NCAR/openiotwx-stl/shield/pineapple_shield_MF.stl

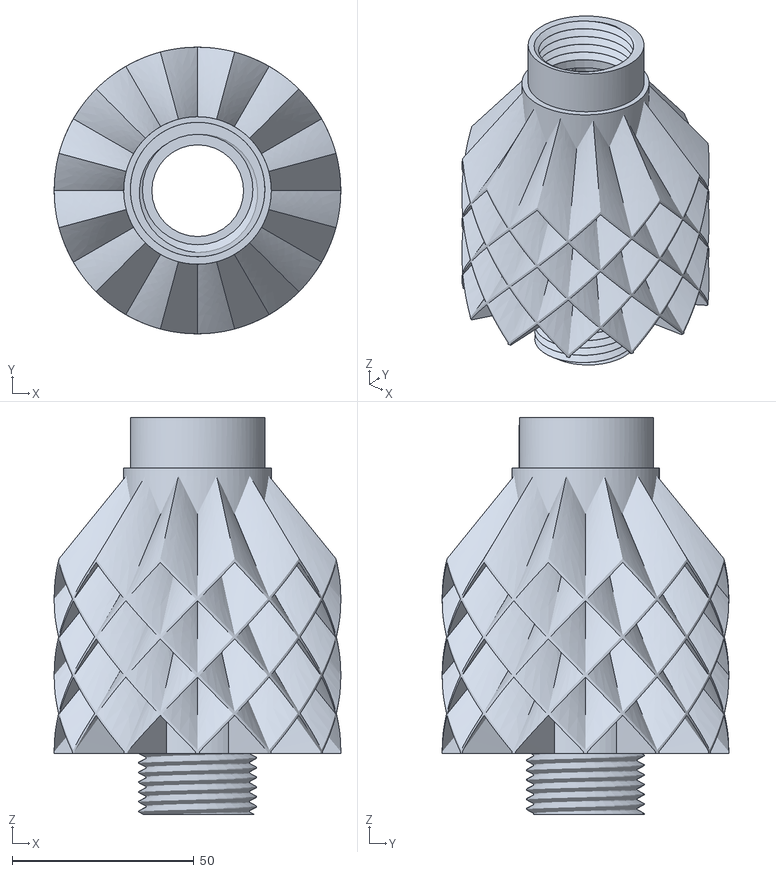
[picture p15: CAD file, 2023-07-29]
shield/pineapple_shield_MF.stl
78.9 x 78.9 x 109.2
