NCAR/openiotwx-stl/uv/uv_tube_F.stl

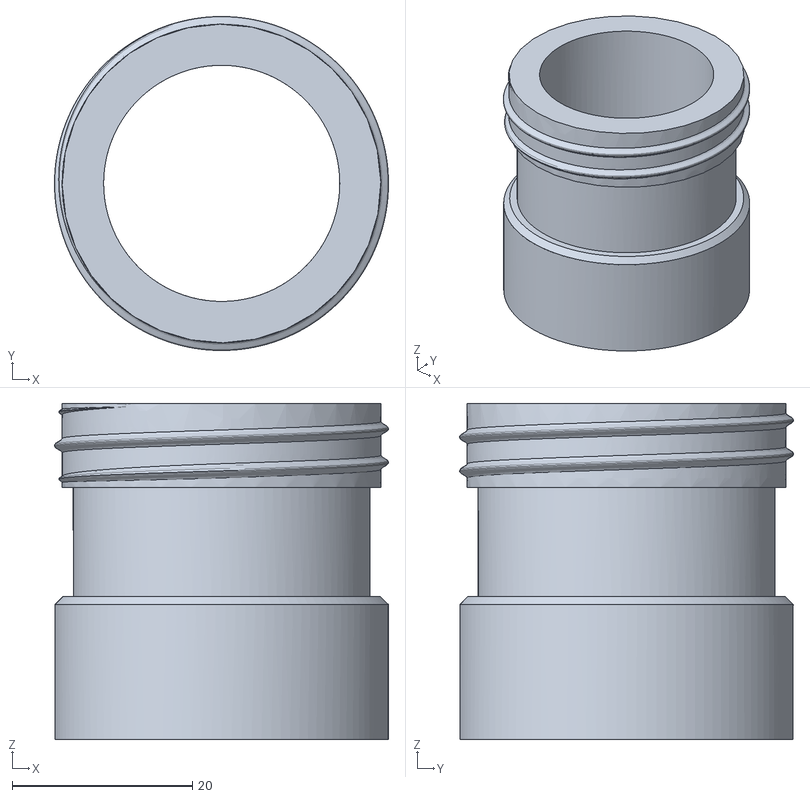
[picture p16: CAD file, 2023-07-29]
uv/uv_tube_F.stl
37.1 x 37.1 x 37.3
