NCAR/openiotwx-stl/accessories/sensor_stand/Center Column.stl

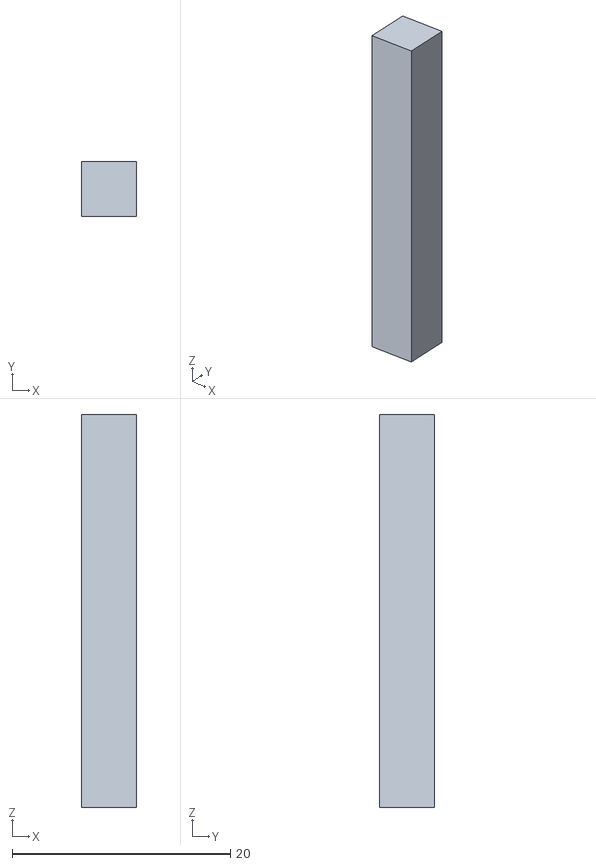
[picture p17: CAD file, 2024-05-13]
accessories/sensor_stand/Center Column.stl
5.00 x 5.00 x 36.0
