NCAR/openiotwx-stl/aq/aq_base_F.stl

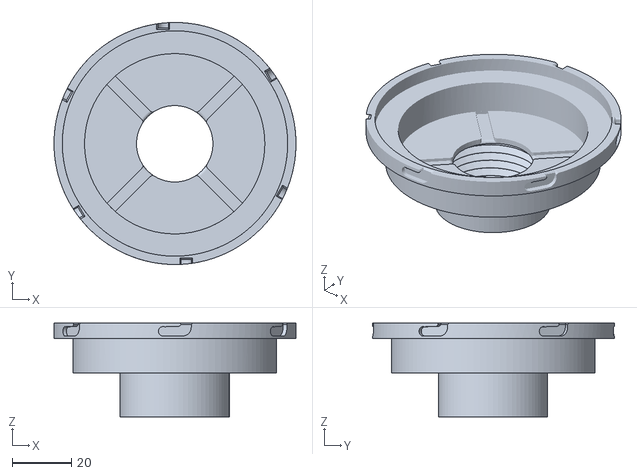
[picture p18: CAD file, 2023-07-29]
aq/aq_base_F.stl
81.9 x 81.9 x 31.8
