NCAR/openiotwx-stl/endcaps/vented_endcap.stl

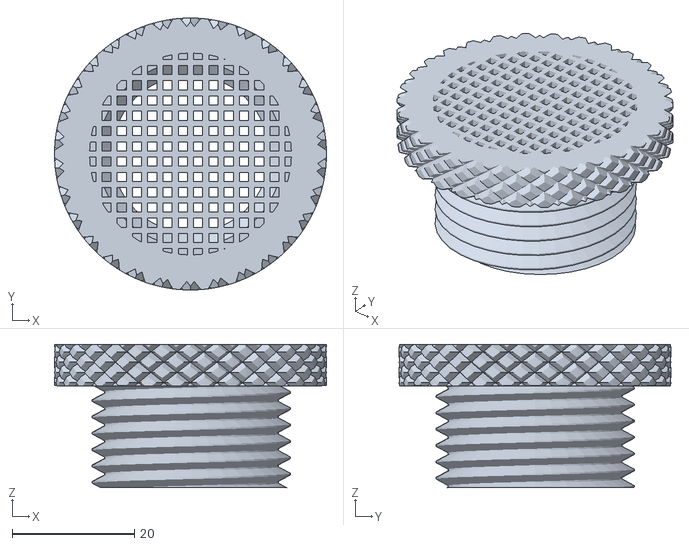
[picture p19: CAD file, 2023-07-29]
endcaps/vented_endcap.stl
44.5 x 44.5 x 23.4
