NCAR/openiotwx-stl/housing/orb45_housing_5open.stl

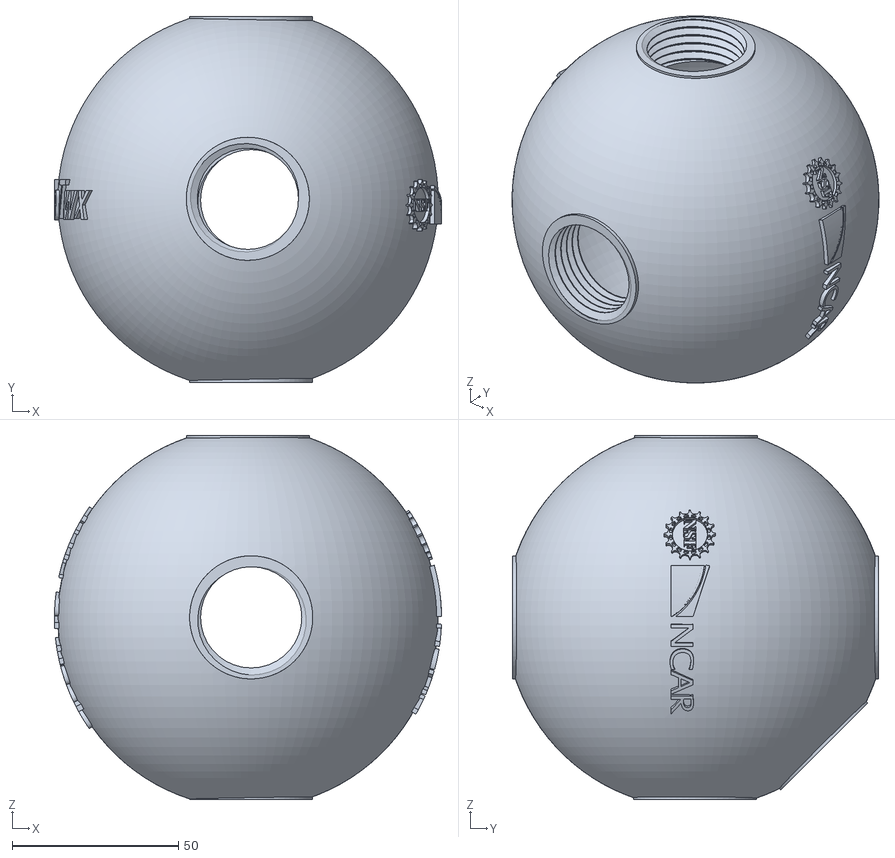
[picture p20: CAD file, 2023-07-29]
housing/orb45_housing_5open.stl
116.3 x 110.0 x 109.5
