NCAR/openiotwx-stl/uv/uv_topcap.stl

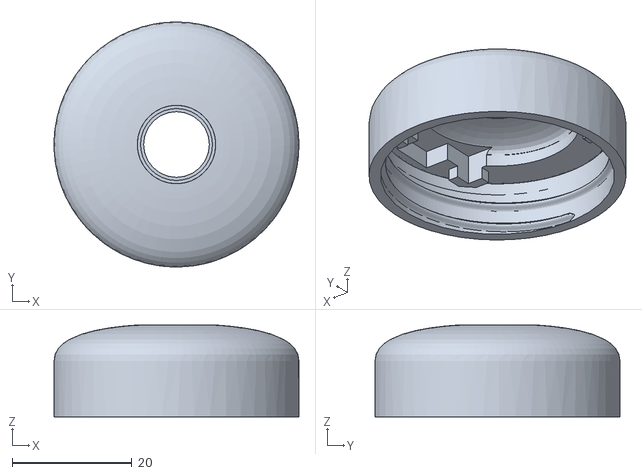
[picture p21: CAD file, 2023-07-29]
uv/uv_topcap.stl
41.0 x 41.0 x 15.4
