NCAR/openiotwx-stl/aq/aq_hood_connecting_MF.stl

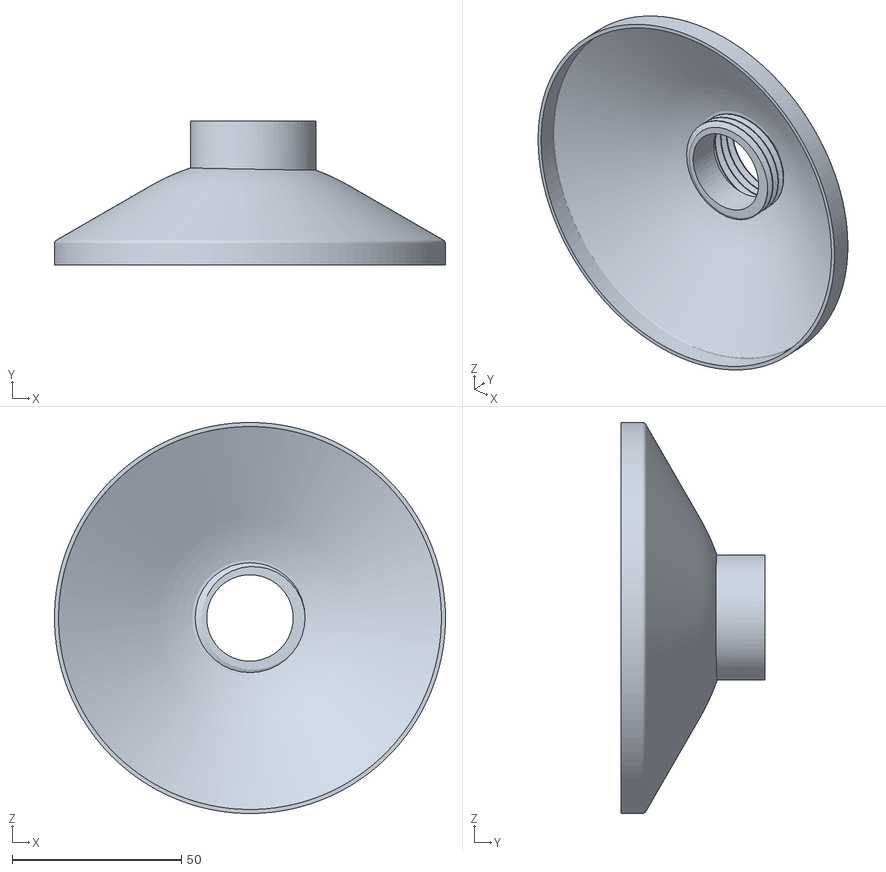
[picture p22: CAD file, 2023-07-29]
aq/aq_hood_connecting_MF.stl
115.4 x 42.4 x 115.4
