NCAR/openiotwx-stl/housing/orb38_housing_4open.stl

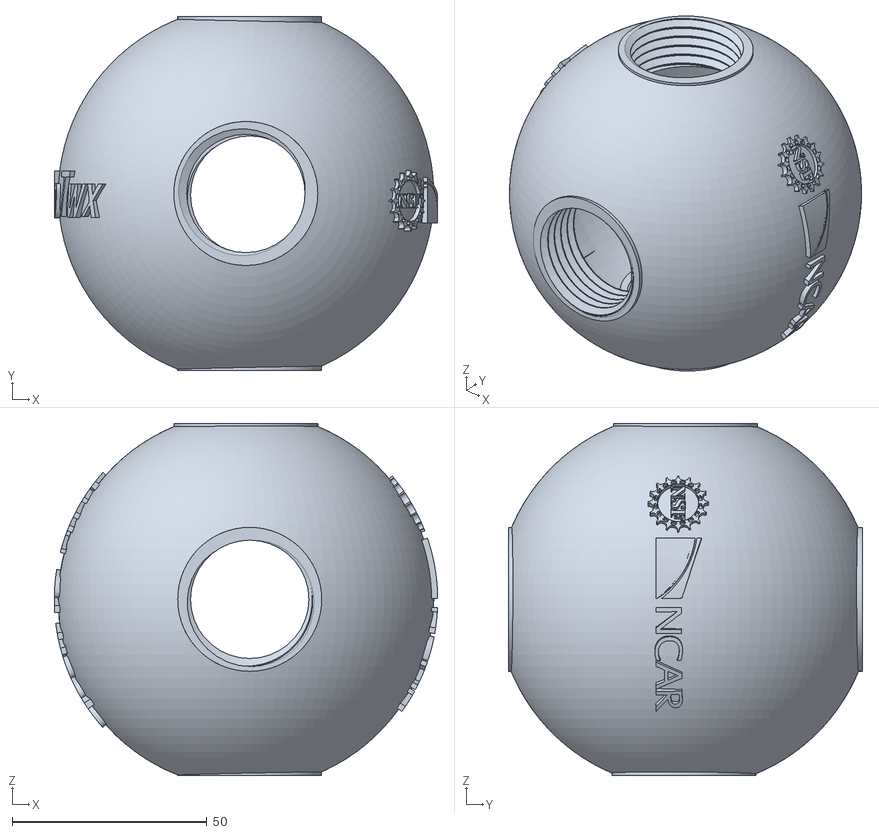
[picture p23: CAD file, 2023-07-29]
housing/orb38_housing_4open.stl
98.5 x 91.0 x 90.5
