NCAR/openiotwx-stl/aq/aq_vented_locking_lid_M.stl

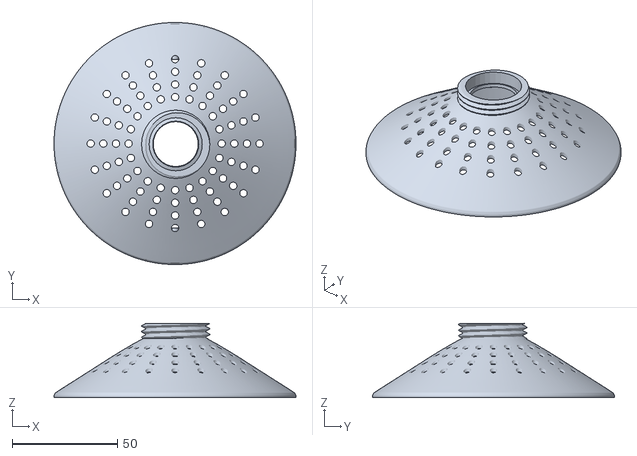
[picture p24: CAD file, 2023-07-29]
aq/aq_vented_locking_lid_M.stl
114.9 x 114.9 x 35.2
