NCAR/openiotwx-stl/aq/aq_base_M.stl

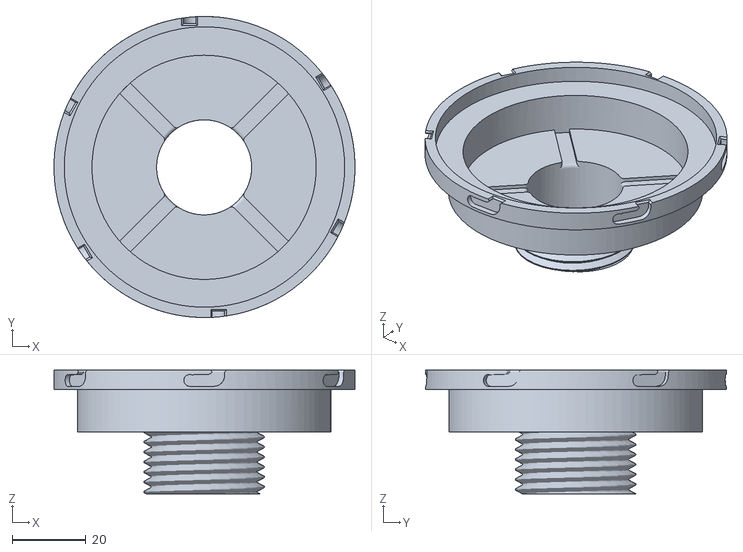
[picture p25: CAD file, 2023-07-29]
aq/aq_base_M.stl
81.9 x 81.9 x 33.7
