NCAR/openiotwx-stl/aq/aq_vented_locking_lid_F.stl

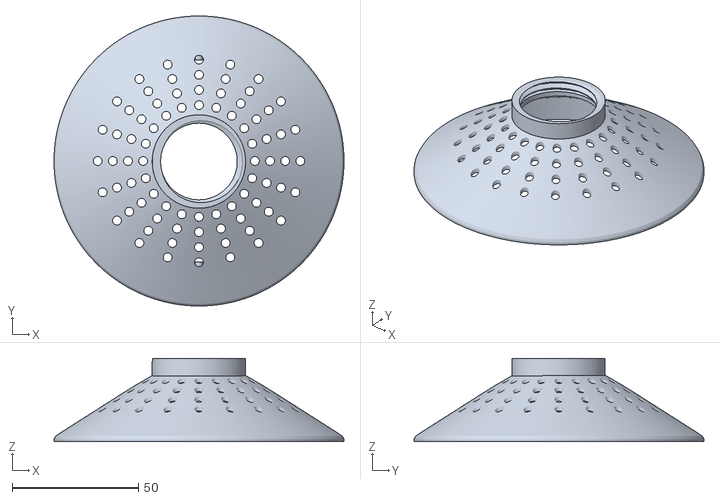
[picture p26: CAD file, 2023-07-29]
aq/aq_vented_locking_lid_F.stl
114.9 x 114.9 x 33.0
