NCAR/openiotwx-stl/aq/aq_hood_terminating_F.stl

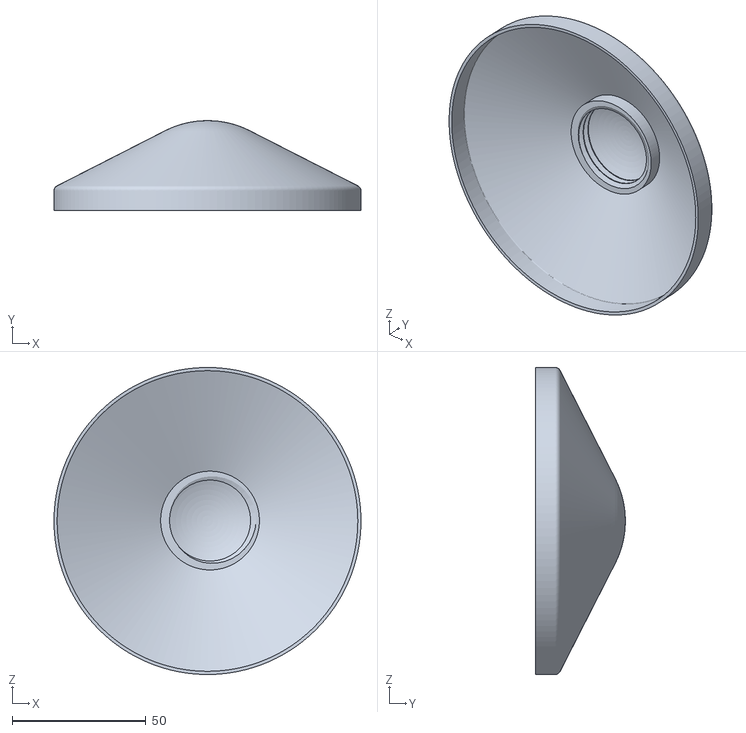
[picture p27: CAD file, 2023-07-29]
aq/aq_hood_terminating_F.stl
115.0 x 33.6 x 115.0
