NCAR/openiotwx-stl/aq/aq_hood_terminating_M.stl

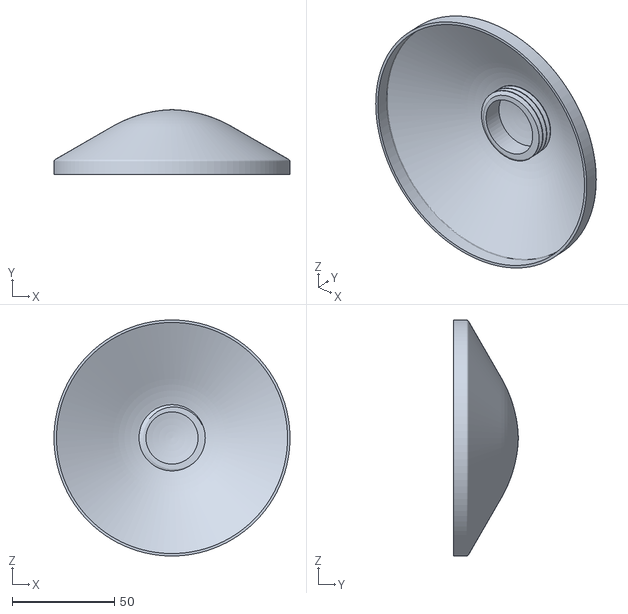
[picture p28: CAD file, 2023-07-29]
aq/aq_hood_terminating_M.stl
115.4 x 31.7 x 115.4
