NCAR/openiotwx-stl/aq/aq_hood_connecting_FM.stl

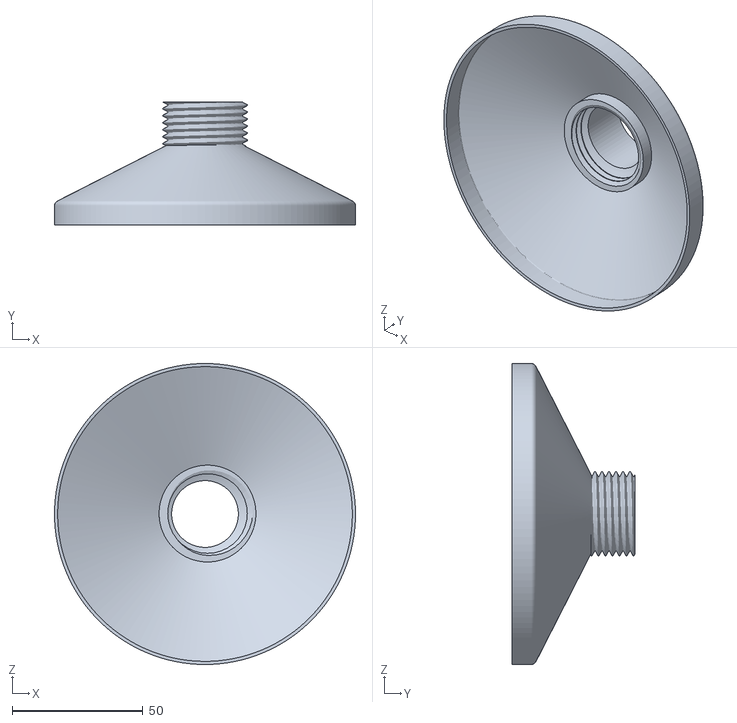
[picture p29: CAD file, 2023-07-29]
aq/aq_hood_connecting_FM.stl
115.0 x 47.0 x 115.0
