NCAR/openiotwx-stl/aq/aq_hood_connecting_MM.stl

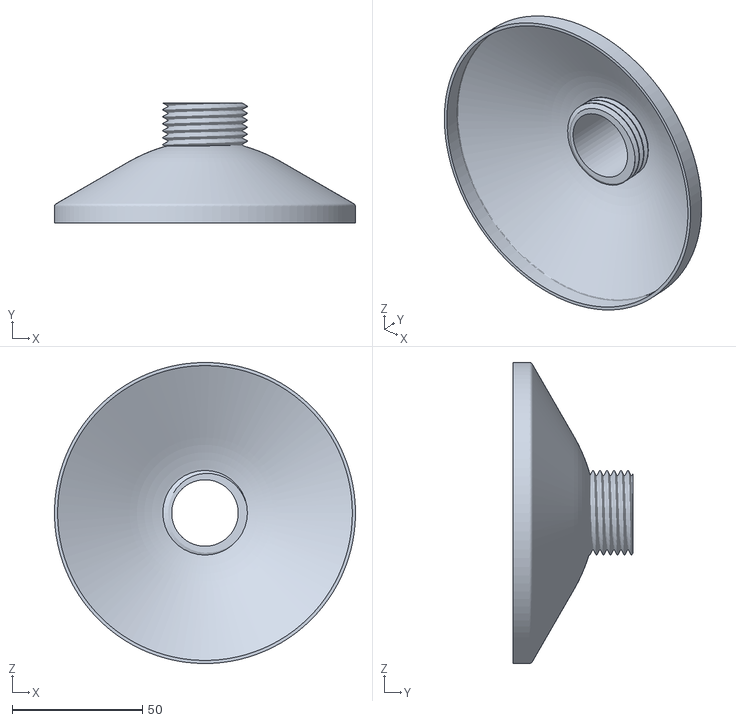
[picture p30: CAD file, 2023-07-29]
aq/aq_hood_connecting_MM.stl
115.4 x 45.9 x 115.4
