NCAR/openiotwx-stl/aq/aq_hood_connecting_FF.stl

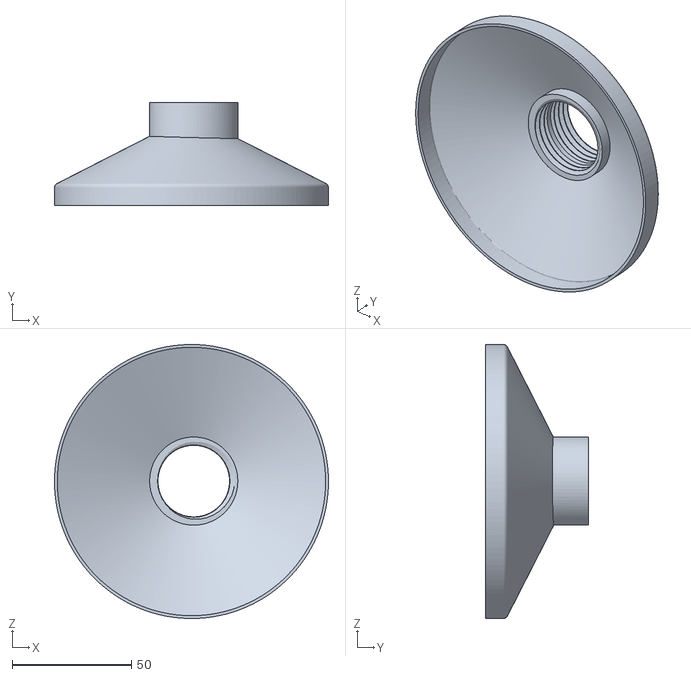
[picture p31: CAD file, 2023-07-29]
aq/aq_hood_connecting_FF.stl
115.0 x 43.0 x 115.0
